Rookwork/EXPress/cutting_arcade_stick_art/readme_assets/cut-half.jpeg

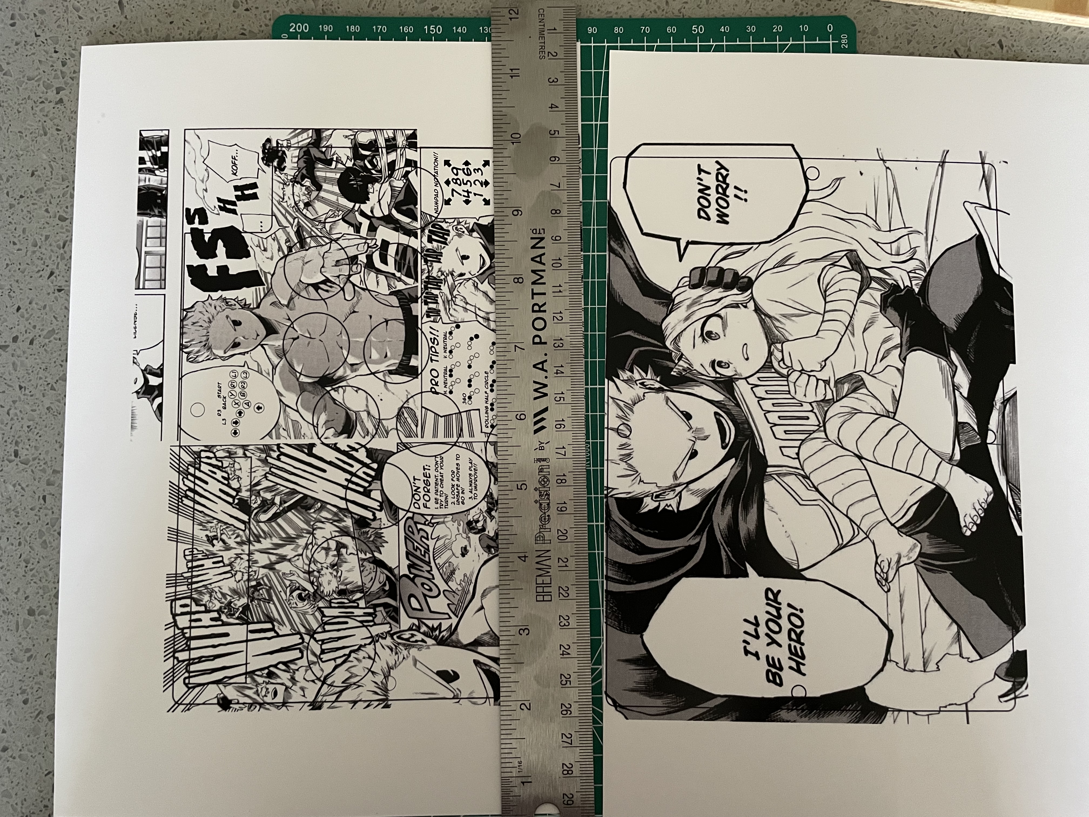
cutting_arcade_stick_art/readme_assets/cut-half.jpeg
